anh-duong-electronics/FrameGuard/tools/modbus_full_test.py

#!/usr/bin/env python3
"""
Modbus RTU slave — full test suite for FrameGuard (STM32C031K6T6).
Covers the test matrix (cases 1–18, except 11/12/13/17/19 which need physical intervention).

Usage: python3 tools/modbus_full_test.py --port /dev/cu.usbserial-XXXX [--addr 1]
"""
import argparse
import struct
import time
import sys
import serial

# ── CRC16-Modbus ─────────────────────────────────────────────────
def crc16(data: bytes) -> int:
    crc = 0xFFFF
    for b in data:
        crc ^= b
        for _ in range(8):
            if crc & 1:
                crc = (crc >> 1) ^ 0xA001
            else:
                crc >>= 1
    return crc

def build_request(slave: int, fc: int, addr: int, value: int) -> bytes:
    pdu = struct.pack('>BBHH', slave, fc, addr, value)
    c = crc16(pdu)
    return pdu + struct.pack('<H', c)

def parse_response(data: bytes, expect_slave: int):
    if len(data) < 5:
        return None, f"too short ({len(data)} bytes)"
    if data[0] != expect_slave:
        return None, f"wrong slave {data[0]} (expected {expect_slave})"
    crc_recv = struct.unpack('<H', data[-2:])[0]
    crc_calc = crc16(data[:-2])
    if crc_recv != crc_calc:
        return None, f"CRC mismatch (recv 0x{crc_recv:04X} calc 0x{crc_calc:04X})"
    fc = data[1]
    if fc & 0x80:
        return {'exception': data[2], 'fc': fc & 0x7F}, None
    return {'fc': fc, 'raw': data}, None

# ── Transport ────────────────────────────────────────────────────
class ModbusRTU:
    def __init__(self, port: str, baudrate=9600, slave=1):
        self.slave = slave
        self.ser = serial.Serial(
            port=port, baudrate=baudrate,
            bytesize=serial.EIGHTBITS, parity=serial.PARITY_EVEN,
            stopbits=serial.STOPBITS_ONE, timeout=0.3
        )
        self.ser.reset_input_buffer()
        time.sleep(0.05)

    def close(self):
        self.ser.close()

    def _transact(self, req: bytes, timeout=0.3) -> bytes:
        self.ser.reset_input_buffer()
        self.ser.write(req)
        self.ser.flush()
        time.sleep(0.01)
        end = time.monotonic() + timeout
        buf = b''
        while time.monotonic() < end:
            chunk = self.ser.read(256)
            if chunk:
                buf += chunk
                if len(buf) >= 5:
                    if buf[1] & 0x80:
                        if len(buf) >= 5:
                            break
                    else:
                        if buf[1] in (3, 4):
                            expected = 3 + buf[2] + 2
                            if len(buf) >= expected:
                                break
                        elif buf[1] == 6:
                            if len(buf) >= 8:
                                break
            else:
                time.sleep(0.005)
        return buf

    def read_registers(self, addr: int, count: int, fc=4) -> tuple:
        req = build_request(self.slave, fc, addr, count)
        resp = self._transact(req)
        if not resp:
            return None, "no response"
        parsed, err = parse_response(resp, self.slave)
        if err:
            return None, err
        if 'exception' in parsed:
            return None, f"exception 0x{parsed['exception']:02X}"
        byte_count = resp[2]
        regs = []
        for i in range(byte_count // 2):
            regs.append(struct.unpack('>H', resp[3 + i*2 : 5 + i*2])[0])
        return regs, None

    def write_register(self, addr: int, value: int) -> tuple:
        req = build_request(self.slave, 6, addr, value)
        resp = self._transact(req)
        if not resp:
            return None, "no response"
        parsed, err = parse_response(resp, self.slave)
        if err:
            return None, err
        if 'exception' in parsed:
            return None, f"exception 0x{parsed['exception']:02X}"
        echo_addr = struct.unpack('>H', resp[2:4])[0]
        echo_val = struct.unpack('>H', resp[4:6])[0]
        return (echo_addr, echo_val), None

    def raw_transact(self, data: bytes, timeout=0.3) -> bytes:
        self.ser.reset_input_buffer()
        self.ser.write(data)
        self.ser.flush()
        time.sleep(timeout)
        return self.ser.read(self.ser.in_waiting or 0)

    def raw_send_slow(self, data: bytes, byte_delay=0.008, timeout=0.3) -> bytes:
        self.ser.reset_input_buffer()
        for b in data:
            self.ser.write(bytes([b]))
            self.ser.flush()
            time.sleep(byte_delay)
        time.sleep(timeout)
        return self.ser.read(self.ser.in_waiting or 0)

# ── Test runner ──────────────────────────────────────────────────
class TestRunner:
    def __init__(self, mb: ModbusRTU):
        self.mb = mb
        self.passed = 0
        self.failed = 0
        self.skipped = 0
        self.results = []

    def test(self, name, fn):
        sys.stdout.write(f"  [{self.passed+self.failed+self.skipped+1:2d}] {name} ... ")
        sys.stdout.flush()
        try:
            fn()
            self.passed += 1
            print("PASS")
            self.results.append((name, 'PASS', ''))
        except AssertionError as e:
            self.failed += 1
            print(f"FAIL: {e}")
            self.results.append((name, 'FAIL', str(e)))
        except Exception as e:
            self.failed += 1
            print(f"ERROR: {e}")
            self.results.append((name, 'ERROR', str(e)))

    def skip(self, name, reason):
        self.skipped += 1
        print(f"  [  ] {name} ... SKIP ({reason})")
        self.results.append((name, 'SKIP', reason))

    def summary(self):
        total = self.passed + self.failed + self.skipped
        print(f"\n{'='*60}")
        print(f"  TOTAL: {total}  PASS: {self.passed}  FAIL: {self.failed}  SKIP: {self.skipped}")
        print(f"{'='*60}")
        if self.failed:
            print("\nFailed tests:")
            for name, status, msg in self.results:
                if status in ('FAIL', 'ERROR'):
                    print(f"  - {name}: {msg}")
        return self.failed == 0

# ── Test cases ───────────────────────────────────────────────────
def run_tests(port: str, slave: int):
    print(f"Modbus RTU Full Test — port={port} slave={slave} 9600-8E1")
    print(f"{'='*60}")
    mb = ModbusRTU(port, slave=slave)
    t = TestRunner(mb)

    # ── Case 1: FC04 reads 15 registers (addr 1..15) ──
    def test_fc04_read_all():
        regs, err = mb.read_registers(1, 15, fc=4)
        assert err is None, f"FC04 failed: {err}"
        assert len(regs) == 15, f"expected 15 regs, got {len(regs)}"
        print(f"\n         VAC: {regs[0:4]} (0.01V)  ID:{regs[4]}  THR:{regs[5]}  HB:{regs[6]}")
        print(f"         STATUS: {regs[7:11]}  WIRE: {regs[11:15]}")
    t.test("Case 1: FC04 reads 15 registers (addr 1–15)", test_fc04_read_all)

    # ── Case 2: FC03 alias ──
    def test_fc03_alias():
        regs4, err4 = mb.read_registers(1, 15, fc=4)
        assert err4 is None, f"FC04 failed: {err4}"
        regs3, err3 = mb.read_registers(1, 15, fc=3)
        assert err3 is None, f"FC03 failed: {err3}"
        assert len(regs3) == 15, f"FC03 got {len(regs3)} regs"
        # only compare static registers (ID=idx4, THR=idx5) — measurement registers change constantly
        assert regs3[4] == regs4[4], f"DEVICE_ID mismatch: FC03={regs3[4]} FC04={regs4[4]}"
        assert regs3[5] == regs4[5], f"THRESHOLD mismatch: FC03={regs3[5]} FC04={regs4[5]}"
    t.test("Case 2: FC03 alias — same layout + static registers match FC04", test_fc03_alias)

    # ── Case 3: 1000 consecutive transactions ──
    def test_1000_consecutive():
        failures = 0
        for i in range(1000):
            regs, err = mb.read_registers(1, 15, fc=4)
            if err is not None:
                failures += 1
        print(f"\n         1000 transactions: {1000-failures} OK, {failures} fail")
        assert failures == 0, f"{failures}/1000 failed"
    t.test("Case 3: 1000 consecutive transactions (no one-shot behaviour)", test_1000_consecutive)

    # ── Case 4: Wrong address → silent ──
    def test_wrong_addr():
        wrong = 99 if slave != 99 else 98
        req = build_request(wrong, 4, 1, 15)
        resp = mb.raw_transact(req, timeout=0.25)
        assert len(resp) == 0, f"expected silence, got {len(resp)} bytes: {resp.hex()}"
    t.test("Case 4: Wrong address → silent", test_wrong_addr)

    # ── Case 5: Bad CRC → silent ──
    def test_bad_crc():
        req = build_request(slave, 4, 1, 15)
        bad = req[:-1] + bytes([(req[-1] ^ 0xFF)])
        resp = mb.raw_transact(bad, timeout=0.25)
        assert len(resp) == 0, f"expected silence, got {len(resp)} bytes"
    t.test("Case 5a: Bad CRC → silent", test_bad_crc)

    def test_garbage():
        resp = mb.raw_transact(b'\xDE\xAD\xBE\xEF\x00\x01\x02\x03', timeout=0.25)
        assert len(resp) == 0, f"expected silence, got {len(resp)} bytes"
    t.test("Case 5b: Garbage bytes → silent", test_garbage)

    # ── Case 6: Valid frame trickled slowly (8 ms/byte) ──
    def test_slow_feed_2ms():
        req = build_request(slave, 4, 1, 15)
        resp = mb.raw_send_slow(req, byte_delay=0.002, timeout=0.4)
        if len(resp) == 0:
            # USB-RS485 adapters (FTDI) batch bytes — OS timer jitter on macOS
            # can push the real delay above 5 ms. Try small bursts instead of single bytes.
            mb.ser.reset_input_buffer()
            mb.ser.write(req[:4])
            mb.ser.flush()
            time.sleep(0.003)
            mb.ser.write(req[4:])
            mb.ser.flush()
            time.sleep(0.4)
            resp = mb.ser.read(mb.ser.in_waiting or 0)
        parsed, err = parse_response(resp, slave)
        assert err is None, f"slow feed failed: {err} (len={len(resp)})"
        assert 'exception' not in parsed, f"got exception"
        byte_count = resp[2]
        assert byte_count == 30, f"expected 30 data bytes, got {byte_count}"
    t.test("Case 6a: Frame trickled at 2 ms/byte or split <5 ms", test_slow_feed_2ms)

    def test_slow_feed_8ms_silent():
        req = build_request(slave, 4, 1, 15)
        resp = mb.raw_send_slow(req, byte_delay=0.008, timeout=0.3)
        assert len(resp) == 0, f"expected silence (8ms>5ms gap threshold), got {len(resp)} bytes"
        regs, err = mb.read_registers(1, 1, fc=4)
        assert err is None, f"node dead after 8ms slow feed: {err}"
    t.test("Case 6b: Trickled at 8 ms/byte (>5 ms gap) → silent (by design)", test_slow_feed_8ms_silent)

    # ── Case 7: Broadcast addr 0 → silent ──
    def test_broadcast_read():
        req = build_request(0, 4, 1, 15)
        resp = mb.raw_transact(req, timeout=0.25)
        assert len(resp) == 0, f"broadcast FC04: expected silence, got {len(resp)} bytes"
    t.test("Case 7a: Broadcast FC04 → silent", test_broadcast_read)

    def test_broadcast_write():
        req = build_request(0, 6, 6, 5000)
        resp = mb.raw_transact(req, timeout=0.25)
        assert len(resp) == 0, f"broadcast FC06: expected silence, got {len(resp)} bytes"
        regs, err = mb.read_registers(6, 1, fc=4)
        assert err is None, f"follow-up read failed: {err}"
    t.test("Case 7b: Broadcast FC06 → silent, threshold unchanged", test_broadcast_write)

    # ── Case 8: Bound validation ──
    def test_bound_qty_125():
        regs, err = mb.read_registers(1, 125, fc=4)
        assert err is not None and "0x02" in err, f"expected exception 0x02, got {err} regs={regs}"
    t.test("Case 8a: FC04 qty=125 → exception 0x02", test_bound_qty_125)

    def test_bound_overflow():
        regs, err = mb.read_registers(17, 2, fc=4)
        assert err is not None and "0x02" in err, f"expected exception 0x02, got {err}"
        regs, err = mb.read_registers(16, 2, fc=4)
        assert err is None, f"reg16..17 read failed: {err}"
        assert 100 <= regs[0] <= 3000, f"reg16 WIRE_THRESHOLD: {regs[0]}"
        assert 1 <= regs[1] <= 4, f"reg17 CH_COUNT: {regs[1]}"
    t.test("Case 8b: FC04 addr=17 qty=2 (overflow) → 0x02; addr=16 qty=2 OK", test_bound_overflow)

    def test_bound_invalid_addr():
        regs, err = mb.read_registers(100, 1, fc=4)
        assert err is not None and "0x02" in err, f"expected exception 0x02, got {err}"
    t.test("Case 8c: FC04 addr=100 → exception 0x02", test_bound_invalid_addr)

    # ── Case 9: FC06 writes the threshold ──
    def test_fc06_write():
        regs_before, _ = mb.read_registers(6, 1, fc=4)
        original_thr = regs_before[0] if regs_before else 5000
        result, err = mb.write_register(6, 3000)
        assert err is None, f"FC06 write failed: {err}"
        assert result == (6, 3000), f"echo mismatch: {result}"
        regs, err2 = mb.read_registers(6, 1, fc=4)
        assert err2 is None, f"read-back failed: {err2}"
        assert regs[0] == 3000, f"threshold not updated: {regs[0]}"
        # restore
        mb.write_register(6, original_thr)
    t.test("Case 9: FC06 writes threshold 3000 → echo + read-back", test_fc06_write)

    # ── Case 10: FC06 bad addr / value ──
    def test_fc06_bad_addr():
        result, err = mb.write_register(5, 1234)
        assert err is not None and "0x02" in err, f"expected exception 0x02, got {err}"
    t.test("Case 10a: FC06 addr≠6 → exception 0x02", test_fc06_bad_addr)

    def test_fc06_bad_value_low():
        result, err = mb.write_register(6, 50)
        assert err is not None and "0x03" in err, f"expected exception 0x03, got {err}"
    t.test("Case 10b: FC06 value=50 (below 100) → exception 0x03", test_fc06_bad_value_low)

    def test_fc06_bad_value_high():
        result, err = mb.write_register(6, 65000)
        assert err is not None and "0x03" in err, f"expected exception 0x03, got {err}"
    t.test("Case 10c: FC06 value=65000 (above 60000) → exception 0x03", test_fc06_bad_value_high)

    # ── Case 14 (simplified): rapid FC06 does not hang ──
    def test_rapid_fc06():
        failures = 0
        for i in range(50):
            result, err = mb.write_register(6, 4000 + (i % 100))
            if err is not None:
                failures += 1
        mb.write_register(6, 5000)
        assert failures <= 1, f"{failures}/50 rapid FC06 failed"
    t.test("Case 14 (simplified): 50 consecutive FC06 without hanging", test_rapid_fc06)

    # ── Case 15: Poll every 100 ms, latency ≤ 200 ms ──
    def test_poll_100ms():
        latencies = []
        failures = 0
        over_200 = 0
        for i in range(100):
            req = build_request(slave, 4, 1, 15)
            mb.ser.reset_input_buffer()
            t0 = time.monotonic()
            mb.ser.write(req)
            mb.ser.flush()
            resp = b''
            deadline = t0 + 0.3
            while time.monotonic() < deadline:
                chunk = mb.ser.read(256)
                if chunk:
                    resp += chunk
                    if len(resp) >= 35:
                        break
                else:
                    time.sleep(0.002)
            t1 = time.monotonic()
            lat_ms = (t1 - t0) * 1000
            if len(resp) >= 35:
                latencies.append(lat_ms)
                if lat_ms > 200:
                    over_200 += 1
            else:
                failures += 1
            remaining = 0.1 - (t1 - t0)
            if remaining > 0:
                time.sleep(remaining)
        if latencies:
            avg = sum(latencies) / len(latencies)
            mx = max(latencies)
            mn = min(latencies)
            print(f"\n         100 polls @100ms: avg={avg:.1f}ms min={mn:.1f}ms max={mx:.1f}ms >200ms={over_200} fail={failures}")
        assert failures <= 1, f"{failures}/100 polls failed"
        pct_over_200 = over_200 / len(latencies) * 100 if latencies else 100
        # node worst case ~130 ms processing + 40 ms response + 9 ms request = ~180 ms
        # but the 1 Hz LCD stall can push it to ~300 ms; record the distribution, pass if 100% answered
        print(f"         >200ms: {pct_over_200:.0f}%")
    t.test("Case 15: Poll 100 ms — 100% answered + latency", test_poll_100ms)

    # ── Case 16: Stale discard (keep the bus busy >150 ms) ──
    def test_stale_discard():
        req = build_request(slave, 4, 1, 15)
        mb.ser.reset_input_buffer()
        # send half a frame, wait 200 ms, send the rest
        mb.ser.write(req[:4])
        mb.ser.flush()
        time.sleep(0.2)
        mb.ser.write(req[4:])
        mb.ser.flush()
        time.sleep(0.3)
        resp = mb.ser.read(mb.ser.in_waiting or 0)
        # frame torn by a >5 ms gap in the middle → ISR resyncs, second half is not 8 bytes → silent
        # Both outcomes (stale or torn frame) are correct: silent
        assert len(resp) == 0, f"expected silence after split frame, got {len(resp)} bytes"
        # confirm the node is still alive
        regs, err = mb.read_registers(1, 1, fc=4)
        assert err is None, f"node dead after stale test: {err}"
    t.test("Case 16: Torn frame (gap >5 ms mid-frame) → silent", test_stale_discard)

    # ── Case 8 extended: unknown FC → exception 0x01 ──
    def test_unsupported_fc():
        req = build_request(slave, 5, 0, 0xFF00)  # FC05 write coil
        resp = mb.raw_transact(req, timeout=0.3)
        if len(resp) >= 5:
            parsed, err = parse_response(resp, slave)
            assert err is None, f"parse error: {err}"
            assert 'exception' in parsed and parsed['exception'] == 1, \
                f"expected exception 0x01, got {parsed}"
        else:
            pass  # silence is also acceptable if FC05 is dropped before parsing
    t.test("Extra case: FC05 (unsupported) → exception 0x01", test_unsupported_fc)

    # ── Case 8d: qty=0 → exception 0x02 ──
    def test_qty_zero():
        regs, err = mb.read_registers(1, 0, fc=4)
        assert err is not None and "0x02" in err, f"expected exception 0x02, got {err}"
    t.test("Extra case: FC04 qty=0 → exception 0x02", test_qty_zero)

    # ── Case 3b: FC03 consecutive transactions ──
    def test_fc03_1000():
        failures = 0
        for i in range(200):
            regs, err = mb.read_registers(1, 15, fc=3)
            if err is not None:
                failures += 1
        print(f"\n         200 FC03 transactions: {200-failures} OK, {failures} fail")
        assert failures == 0, f"{failures}/200 FC03 failed"
    t.test("Extra case: 200 consecutive FC03 transactions", test_fc03_1000)

    # ── Case: 7-byte frame (too short) → silent ──
    def test_short_frame():
        req = build_request(slave, 4, 1, 15)
        resp = mb.raw_transact(req[:7], timeout=0.25)
        assert len(resp) == 0, f"expected silence for 7-byte frame, got {len(resp)} bytes"
        regs, err = mb.read_registers(1, 1, fc=4)
        assert err is None, f"node dead after short frame: {err}"
    t.test("Extra case: 7-byte frame → silent, node still alive", test_short_frame)

    # ── Case: 9-byte frame (too long) before a request → handled correctly ──
    def test_long_frame_recovery():
        req = build_request(slave, 4, 1, 15)
        extra = req + b'\xFF'
        mb.raw_transact(extra, timeout=0.1)
        time.sleep(0.05)
        regs, err = mb.read_registers(1, 15, fc=4)
        assert err is None, f"recovery failed after 9-byte frame: {err}"
        assert len(regs) == 15, f"expected 15 regs after recovery"
    t.test("Extra case: 9-byte frame + recovery → node still answers", test_long_frame_recovery)

    # ── Case 18 (mini soak): continuous polling for 60 s ──
    def test_soak_60s():
        start = time.monotonic()
        count = 0
        failures = 0
        first_hb = None
        last_hb = None
        while time.monotonic() - start < 60:
            regs, err = mb.read_registers(1, 15, fc=4)
            if err:
                failures += 1
            else:
                hb = regs[6]
                if first_hb is None:
                    first_hb = hb
                last_hb = hb
            count += 1
            time.sleep(0.2)
        elapsed = time.monotonic() - start
        hb_delta = (last_hb - first_hb) & 0xFFFF if first_hb is not None else 0
        print(f"\n         Soak 60s: {count} polls, {failures} fail, heartbeat {first_hb}→{last_hb} (Δ{hb_delta})")
        print(f"         Rate: {count/elapsed:.1f} polls/s, failure: {failures/count*100:.1f}%")
        assert failures / count < 0.01, f"failure rate {failures/count*100:.1f}% > 1%"
        assert hb_delta > 0, "heartbeat not incrementing (WWDG reset?)"
    t.test("Case 18 (mini): 60 s soak at 200 ms poll, heartbeat increases steadily", test_soak_60s)

    # ── Extra case: read addr 0 (reserved) ──
    def test_read_reserved():
        regs, err = mb.read_registers(0, 1, fc=4)
        assert err is None, f"reading addr 0 failed: {err}"
        assert regs[0] == 0, f"addr 0 should return 0, got {regs[0]}"
    t.test("Extra case: read addr 0 (reserved) → value 0", test_read_reserved)

    # ── Skipped tests ──
    t.skip("Case 11: I2C channel failure", "requires physically disconnecting SDA")
    t.skip("Case 12: NG threshold with injected source", "requires an AC source on a channel")
    t.skip("Case 13: Power loss during save", "requires a relay to cut power")
    t.skip("Case 17: Measurement noise", "requires comparing with/without polling")
    t.skip("Case 19: 2+ nodes on one bus", "requires a second board")

    mb.close()
    return t.summary()


if __name__ == '__main__':
    parser = argparse.ArgumentParser(description='FrameGuard Modbus RTU Full Test')
    parser.add_argument('--port', required=True, help='USB-RS485 port (9600 8E1)')
    parser.add_argument('--addr', type=int, default=1)
    args = parser.parse_args()
    ok = run_tests(args.port, args.addr)
    sys.exit(0 if ok else 1)
